3lRuB3n/Control_volumen/Master/recep.py

from usb_hid import devices as dev
from adafruit_hid.consumer_control_code import ConsumerControlCode as CCC
from adafruit_hid.consumer_control import ConsumerControl as CC
import wled, esp
cc = CC(dev)

def envia_hid(st):
    dicc = {"sil":CCC.MUTE,
            "playPau":CCC.PLAY_PAUSE,
            "sig":CCC.SCAN_NEXT_TRACK,
            "ant":CCC.SCAN_PREVIOUS_TRACK,
            "volMen":CCC.VOLUME_DECREMENT,
            "volMas":CCC.VOLUME_INCREMENT,
            "onOff":113 #Creo que fn+f5
            }
    cc.send(dicc.get(st))

def envia_audio(dif, recep):
    codigo = "volMas" if dif > 0 else "volMen"
    for i in range(abs(dif)):
        recep.envia(codigo)

class recep:
    def __init__(self, Dir, MAC, img, letra): #Dir: Protocolo; MAC: dirección MAC, '0' si no corresponde; img: indice en la spritesheet; letra: posición en los dispositivos espnow, de la 'a' a la 't' segun se declaren
        self.dir = Dir
        self.img = img #posicion del sprite del receptor en el spritsheet
        self.mac = MAC
        self.letra = letra
        if Dir == "USB":
            self.envia = envia_hid
        elif Dir == "test":
            self.envia = print
        elif Dir == "wled":
            self.envia = wled.envia_wled
        elif Dir == "ESPNow":
            self.envia = esp.envia_espnow
